mohamedboubaker/Battery-Powered-STM32-Board-With-USB/Hardware/Pictures/3d front.png

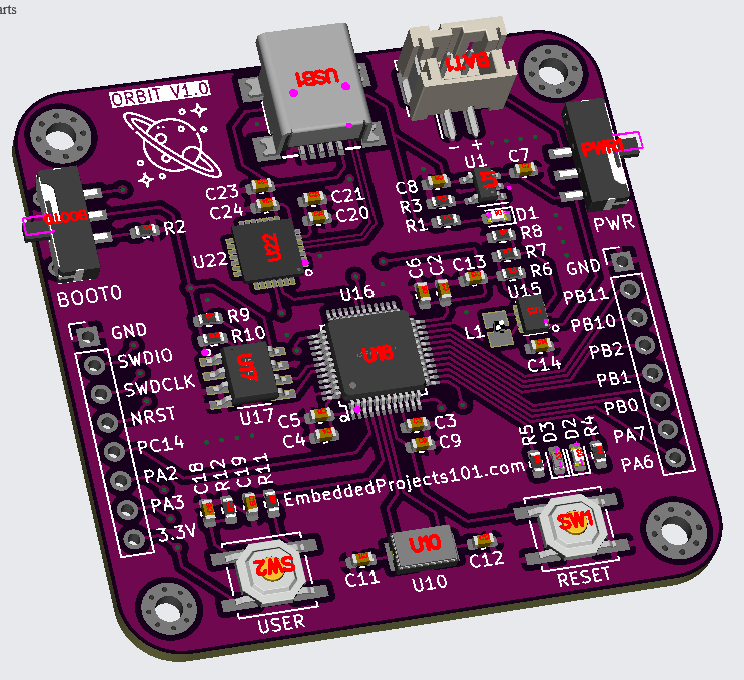
Hardware/Pictures/3d front.png
