mohamedboubaker/Battery-Powered-STM32-Board-With-USB/Hardware/Pictures/Bottom Side PCB.png

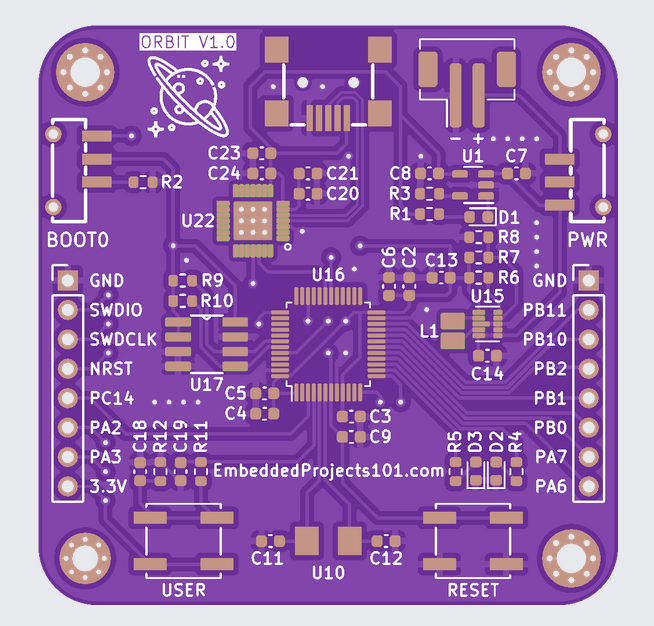
Hardware/Pictures/Bottom Side PCB.png
