mohamedboubaker/Battery-Powered-STM32-Board-With-USB/Hardware/Pictures/Circuit diagram-1.png

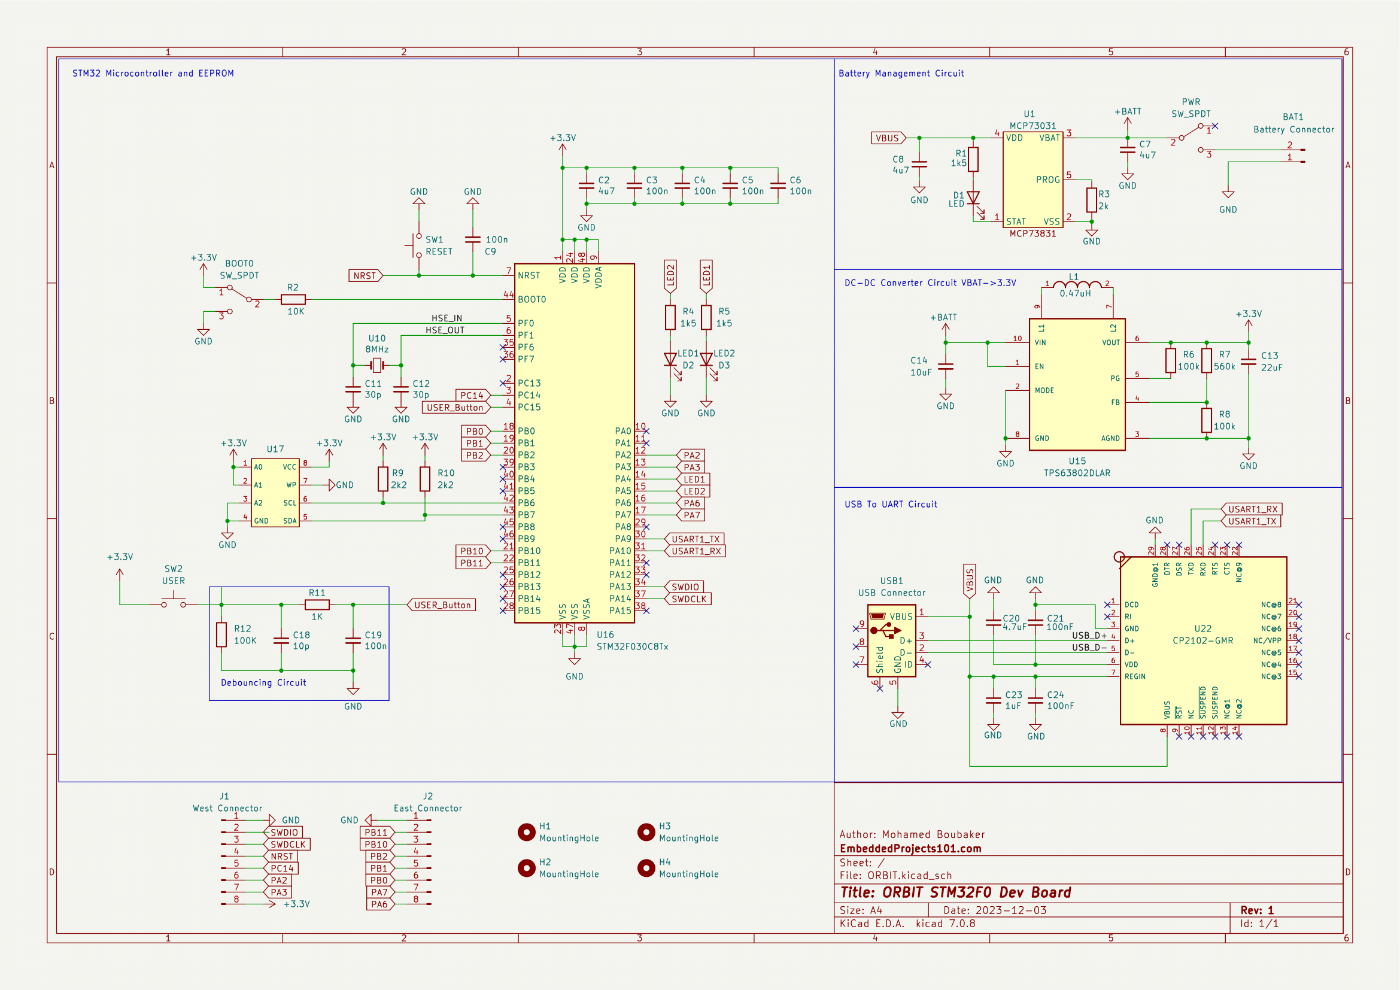
Hardware/Pictures/Circuit diagram-1.png
