mohamedboubaker/Battery-Powered-STM32-Board-With-USB/Hardware/Pictures/CP2102 connection diagram.png

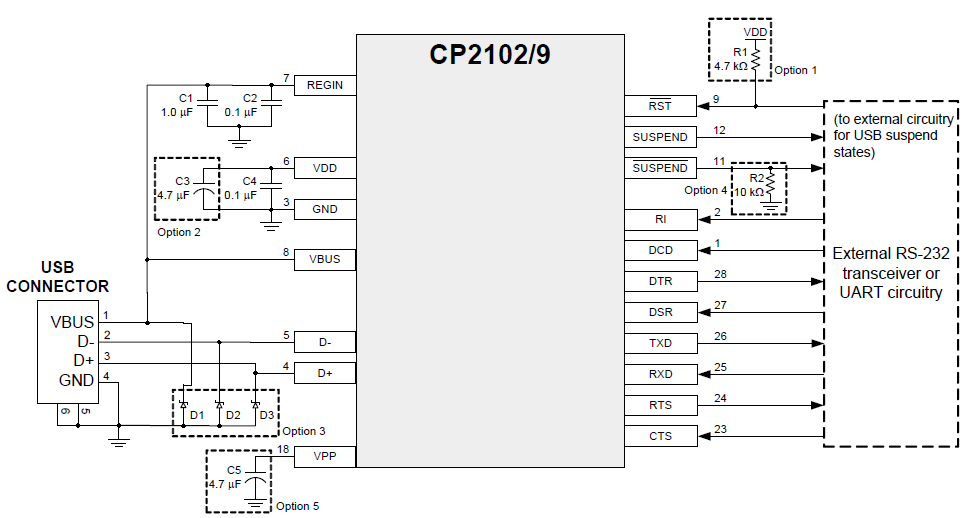
Hardware/Pictures/CP2102 connection diagram.png
