mohamedboubaker/Battery-Powered-STM32-Board-With-USB/Hardware/Pictures/cp2102-usb-to-uart-circuit.png

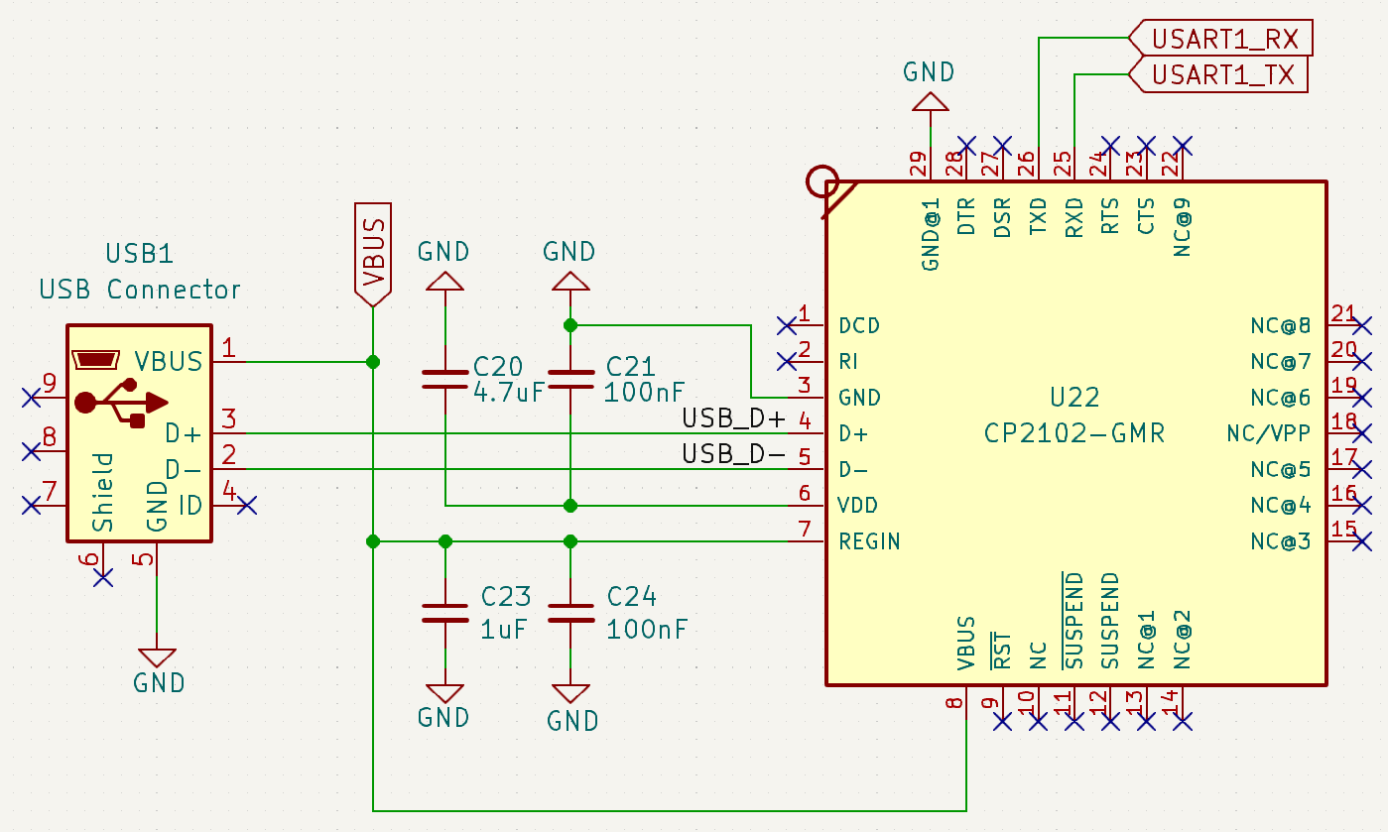
Hardware/Pictures/cp2102-usb-to-uart-circuit.png
