mohamedboubaker/Battery-Powered-STM32-Board-With-USB/Hardware/Pictures/ORBIT PCB backside.png

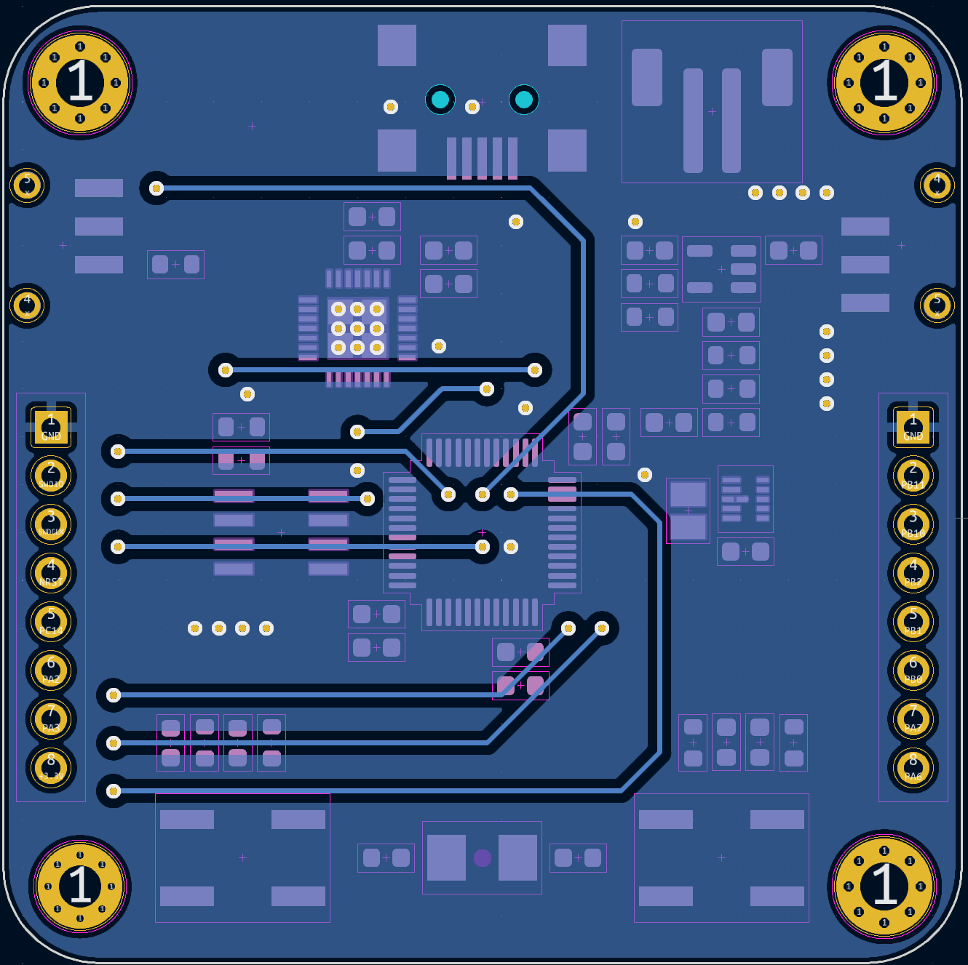
Hardware/Pictures/ORBIT PCB backside.png
