mohamedboubaker/Battery-Powered-STM32-Board-With-USB/Hardware/Pictures/stm32-eeprom-circuit.png

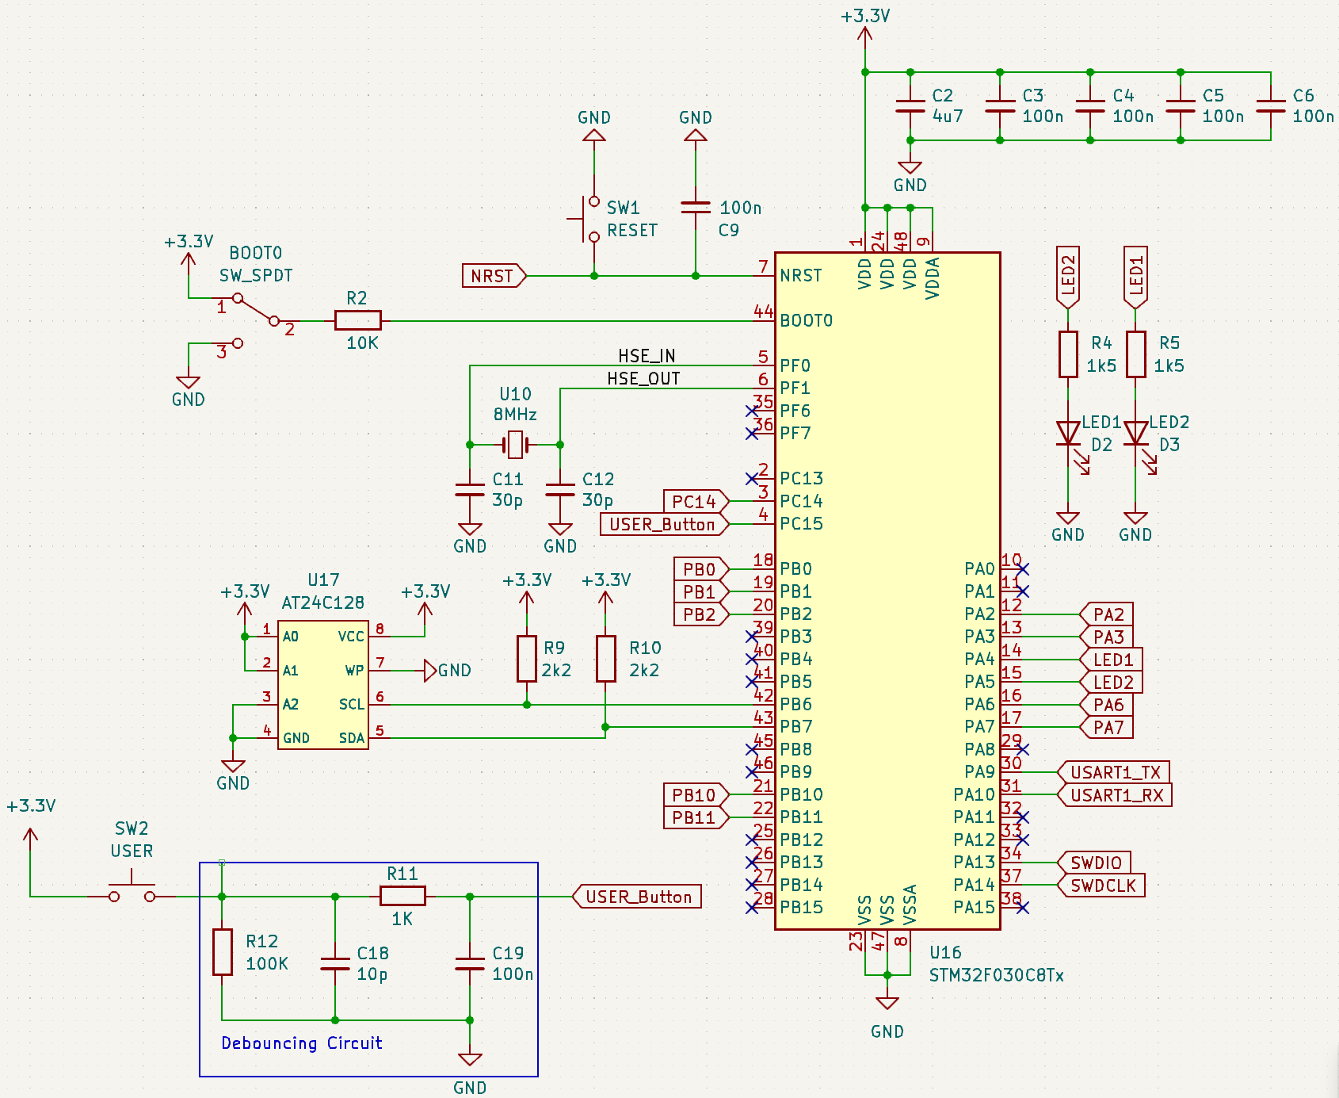
Hardware/Pictures/stm32-eeprom-circuit.png
