mohamedboubaker/Battery-Powered-STM32-Board-With-USB/Hardware/Pictures/STM32CubeProgrammer.png

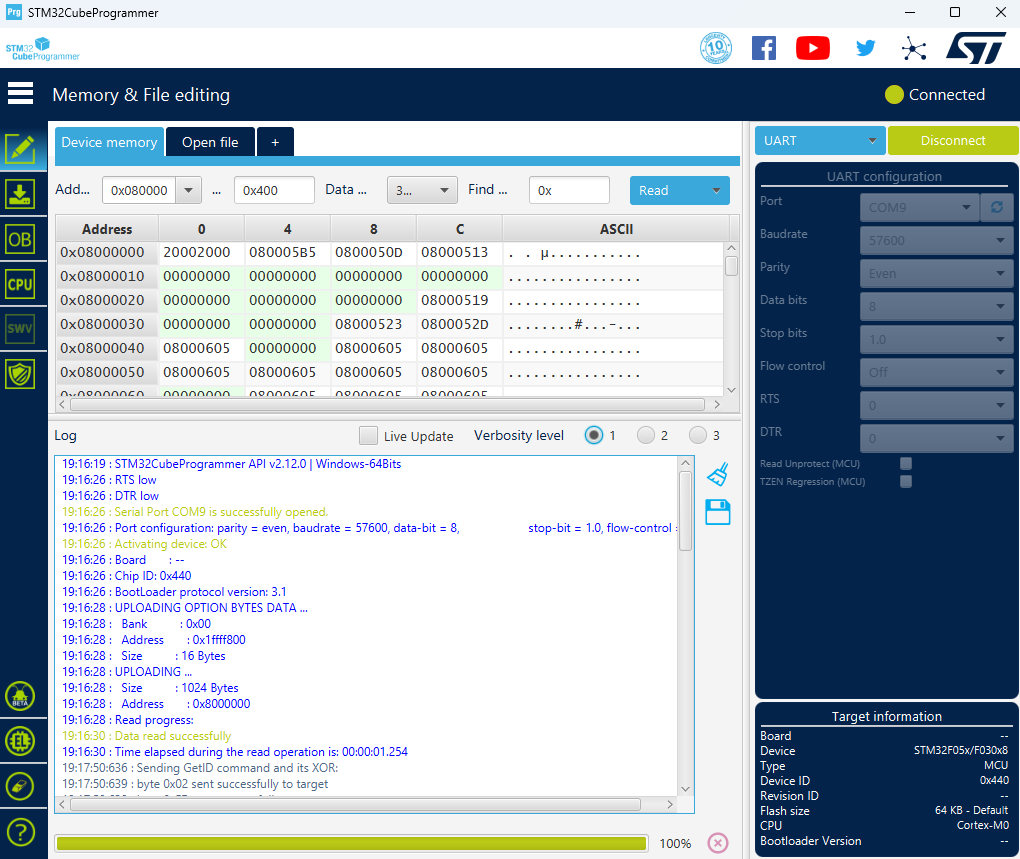
Hardware/Pictures/STM32CubeProgrammer.png
