mohamedboubaker/Battery-Powered-STM32-Board-With-USB/Hardware/Pictures/TPS63802-dc-dc-converter.png

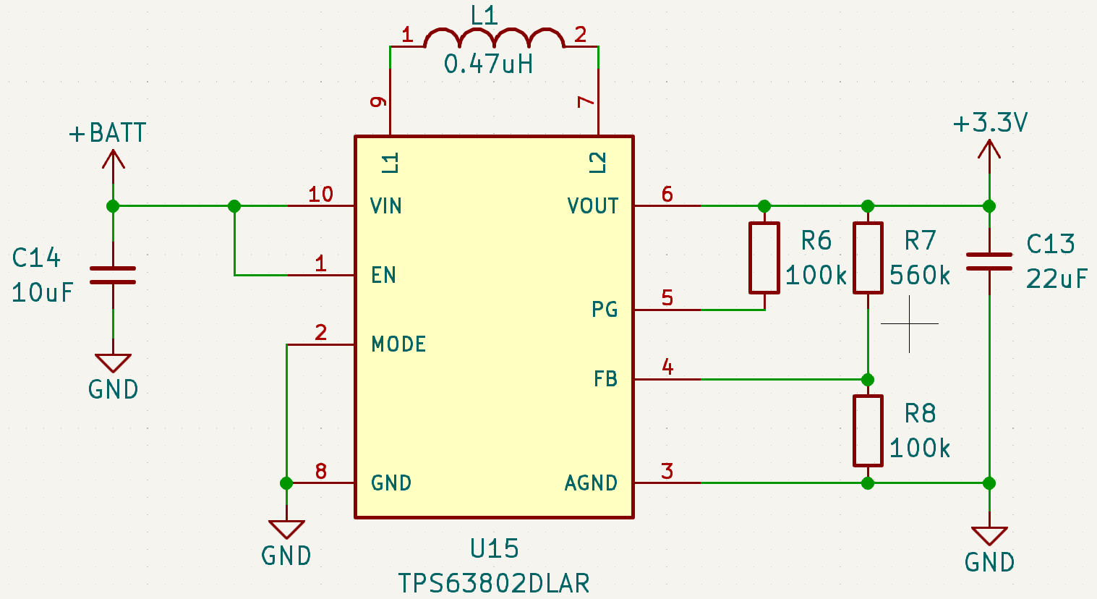
Hardware/Pictures/TPS63802-dc-dc-converter.png
